evezor/v0_5up_digital_input_board/pics/20201102_162934.jpg

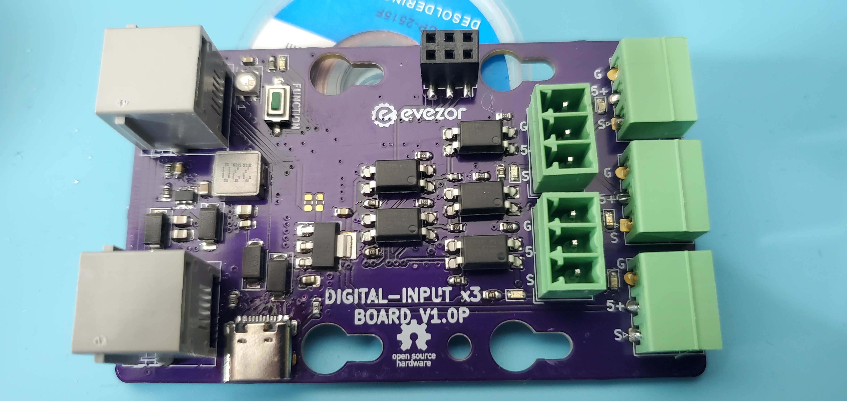
pics/20201102_162934.jpg
